baoqi-zhong/Arduino_clock/Version_2/pic/0.jpg

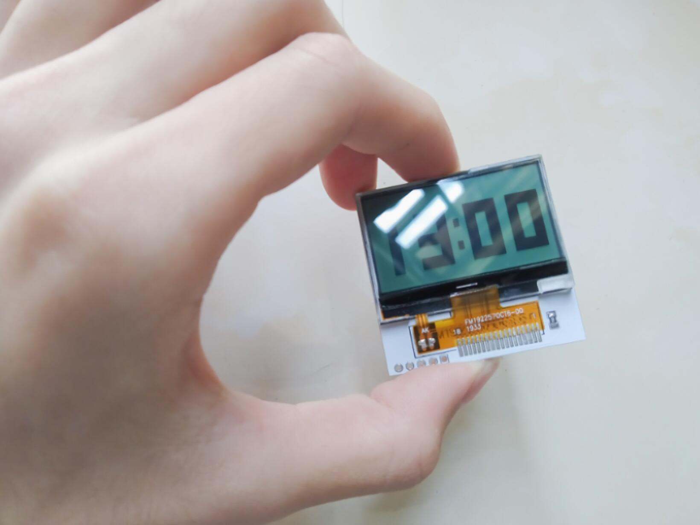
Version_2/pic/0.jpg
