baoqi-zhong/Arduino_clock/Version_2/pic/1.jpg

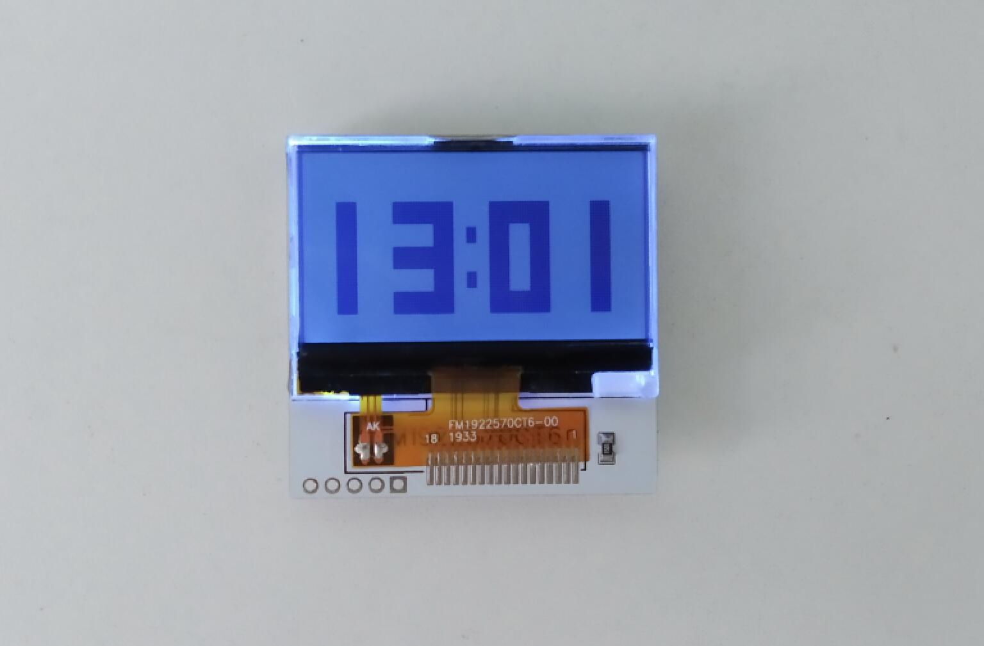
Version_2/pic/1.jpg
